drabenstadtj/musicplayer/ui/screens.py

import curses
import unicodedata
from ui.theme import *
from player.album_art import AlbumArtDisplay
from player.bluetooth import BluetoothManager

def display_width(text):
    """Calculate the display width of a string, accounting for wide characters"""
    width = 0
    for char in text:
        if unicodedata.east_asian_width(char) in ('F', 'W'):
            width += 2  # Full-width or Wide characters
        else:
            width += 1  # Normal width
    return width

def truncate_to_width(text, max_width):
    """Truncate text to fit within max_width, accounting for wide characters"""
    if display_width(text) <= max_width:
        return text

    current_width = 0
    result = ""
    ellipsis = "..."
    ellipsis_width = display_width(ellipsis)

    for char in text:
        char_width = 2 if unicodedata.east_asian_width(char) in ('F', 'W') else 1
        if current_width + char_width + ellipsis_width > max_width:
            return result + ellipsis
        result += char
        current_width += char_width

    return result

class BaseScreen:
    """Base class for all screens"""
    def __init__(self, stdscr):
        self.stdscr = stdscr
        self.height, self.width = stdscr.getmaxyx()
        self._pending_action = None

    def draw_status_bar(self, text, battery_percent=None):
        """Draw status bar at top"""
        self.stdscr.addstr(0, 0, " " * (self.width - 1))
        self.stdscr.addstr(0, 2, text, curses.color_pair(COLOR_STATUS) | curses.A_BOLD)

        if battery_percent is not None:
            battery_text = f"{battery_percent}% {SYMBOL_BATTERY}"
            self.stdscr.addstr(0, self.width - len(battery_text) - 2,
                             battery_text, curses.color_pair(COLOR_STATUS))

    def draw_footer(self, btn1="", btn2="", btn3="", btn4=""):
        """Draw footer with evenly spaced GPIO button labels

        Displays 4 button actions evenly spaced across the bottom
        to match the physical GPIO button layout (left to right).
        """
        footer_y = self.height - 1
        self.stdscr.addstr(footer_y, 0, " " * (self.width - 1))

        labels = [btn1, btn2, btn3, btn4]

        # Calculate positions to distribute evenly across the width
        # Place at 1/8, 3/8, 5/8, 7/8 of width (centered in each quarter)
        positions = [
            self.width // 8,
            (self.width * 3) // 8,
            (self.width * 5) // 8,
            (self.width * 7) // 8
        ]

        for i, label in enumerate(labels):
            if label:  # Only show if label is provided
                # Center the label at its position
                x_pos = positions[i] - len(label) // 2
                x_pos = max(0, min(x_pos, self.width - len(label) - 1))
                try:
                    self.stdscr.addstr(footer_y, x_pos, label)
                except:
                    pass  # Ignore if text doesn't fit

    def draw(self):
        """Override this in subclasses"""
        pass

    def handle_input(self, key):
        """Override this in subclasses. Return False to exit screen."""
        return True
    
    # Button methods - override in subclasses
    def on_up(self):
        """Handle UP button"""
        pass
    
    def on_down(self):
        """Handle DOWN button"""
        pass
    
    def on_select(self):
        """Handle SELECT button"""
        pass
    
    def on_back(self):
        """Handle BACK button"""
        pass


class MainMenuScreen(BaseScreen):
    """Main menu screen"""
    def __init__(self, stdscr):
        super().__init__(stdscr)
        self.menu_items = ["Albums", "Playlists", "Artists", "Settings"]
        self.selected = 0

    def draw(self):
        self.stdscr.clear()
        self.draw_status_bar(f"{SYMBOL_MUSIC} MUSIC PLAYER")

        # Draw menu items
        start_y = 3
        for i, item in enumerate(self.menu_items):
            y = start_y + (i * 2)
            if i == self.selected:
                self.stdscr.addstr(y, 8, f"> {item}",
                                 curses.color_pair(COLOR_SELECTED) | curses.A_BOLD)
            else:
                self.stdscr.addstr(y, 10, item, curses.color_pair(COLOR_NORMAL))

        self.draw_footer("↑", "↓", "Enter", "Quit")
        self.stdscr.refresh()

    def handle_input(self, key):
        if key == curses.KEY_UP:
            self.selected = max(0, self.selected - 1)
        elif key == curses.KEY_DOWN:
            self.selected = min(len(self.menu_items) - 1, self.selected + 1)
        elif key == ord('\n'):  # Enter key
            return self.menu_items[self.selected]  # Return selected menu
        elif key == ord('q') or key == ord('Q'):
            return False
        return True
    
    # Button support
    def on_up(self):
        self.selected = max(0, self.selected - 1)
        self.draw()
    
    def on_down(self):
        self.selected = min(len(self.menu_items) - 1, self.selected + 1)
        self.draw()
    
    def on_select(self):
        self._pending_action = self.menu_items[self.selected]
    
    def on_back(self):
        # On main menu, back does nothing (use long-press to quit)
        pass


class AlbumBrowserScreen(BaseScreen):
    """Album browser screen (full width)"""
    def __init__(self, stdscr, albums):
        super().__init__(stdscr)
        self.albums = albums
        self.album_index = 0
        self.scroll_offset = 0
        self.scroll_frame = 0
        self.last_album_index = 0

    def _get_scrolled_text(self, text, max_width, is_selected):
        """Get scrolling text for selected items with truncated content

        Args:
            text: Text to scroll
            max_width: Maximum display width
            is_selected: Whether this item is selected
        """
        text_width = display_width(text)

        if not is_selected or text_width <= max_width:
            # Not selected or fits within width - no scrolling needed
            return truncate_to_width(text, max_width)

        # Increment scroll offset
        self.scroll_offset = (self.scroll_offset + 1) % (text_width + 3)

        # Create circular scrolling effect
        # Add padding between end and start
        scrolling_text = text + "   " + text

        # Calculate starting position in the scrolling text
        start_offset = self.scroll_offset

        # Extract visible portion
        visible_text = ""
        current_width = 0
        char_index = 0

        # Skip to starting offset
        temp_offset = 0
        while temp_offset < start_offset and char_index < len(scrolling_text):
            char = scrolling_text[char_index]
            char_width = 2 if unicodedata.east_asian_width(char) in ('F', 'W') else 1
            temp_offset += char_width
            char_index += 1

        # Collect visible characters
        while current_width < max_width and char_index < len(scrolling_text):
            char = scrolling_text[char_index]
            char_width = 2 if unicodedata.east_asian_width(char) in ('F', 'W') else 1
            if current_width + char_width > max_width:
                break
            visible_text += char
            current_width += char_width
            char_index += 1

        return visible_text

    def draw(self):
        # Reset scroll if selection changed
        if self.album_index != self.last_album_index:
            self.scroll_offset = 0
            self.scroll_frame = 0
            self.last_album_index = self.album_index

        self.stdscr.clear()
        self.draw_status_bar("Albums")

        # Draw albums (full width)
        self.stdscr.addstr(2, 2, "Albums:", curses.A_BOLD)
        start = max(0, self.album_index - 5)
        for i in range(start, min(len(self.albums), start + 10)):
            y = 4 + (i - start)
            if y >= self.height - 2:
                break

            # Format album display with right-justified artist
            album = self.albums[i]
            artist = album.get('artist', 'Unknown Artist')
            album_name = album['name']

            # Calculate available space (full width)
            is_selected = i == self.album_index
            prefix = "> " if is_selected else "  "
            x_start = 2

            # Calculate max width for content (full width of screen)
            max_line_width = self.width - x_start - 2 - display_width(prefix)

            # Reserve space for artist (right-aligned) - use 40% of width
            artist_width = int(max_line_width * 0.4)
            album_width = max_line_width - artist_width - 1  # -1 for space separator

            # Truncate or scroll artist (right side)
            artist_display = truncate_to_width(artist, artist_width)
            artist_display_width = display_width(artist_display)

            # Display album and artist
            if is_selected:
                # For selected item, check if scrolling is needed
                full_text = f"{album_name} - {artist}"
                full_text_width = display_width(full_text)

                if full_text_width > max_line_width:
                    # Scroll the combined text
                    display_text = self._get_scrolled_text(full_text, max_line_width, True)
                else:
                    # Fits without scrolling - maintain right-justified layout
                    album_display = truncate_to_width(album_name, album_width)
                    album_display_width = display_width(album_display)

                    padding_needed = max_line_width - album_display_width - artist_display_width - 1
                    if padding_needed < 0:
                        padding_needed = 0

                    display_text = album_display + (" " * padding_needed) + " " + artist_display

                self.stdscr.addstr(y, x_start, f"{prefix}{display_text}",
                                 curses.color_pair(COLOR_SELECTED) | curses.A_BOLD)
            else:
                # Not selected - show album left-aligned, artist right-aligned
                album_display = truncate_to_width(album_name, album_width)
                album_display_width = display_width(album_display)

                # Calculate padding to right-justify artist
                padding_needed = max_line_width - album_display_width - artist_display_width - 1
                if padding_needed < 0:
                    padding_needed = 0

                display_text = album_display + (" " * padding_needed) + " " + artist_display

                self.stdscr.addstr(y, x_start, f"{prefix}{display_text}",
                                 curses.color_pair(COLOR_NORMAL))

        self.draw_footer("↑", "↓", "Select", "Back")
        self.stdscr.refresh()

    def handle_input(self, key):
        if key == curses.KEY_UP:
            self.album_index = max(0, self.album_index - 1)

        elif key == curses.KEY_DOWN:
            self.album_index = min(len(self.albums) - 1, self.album_index + 1)

        elif key == ord('\n'):  # Enter
            return ("select_album", self.albums[self.album_index])

        elif key == curses.KEY_BACKSPACE or key == 127:
            return "back"

        elif key == ord('q') or key == ord('Q'):
            return False

        return True

    # Button support
    def on_up(self):
        self.album_index = max(0, self.album_index - 1)
        self.draw()

    def on_down(self):
        self.album_index = min(len(self.albums) - 1, self.album_index + 1)
        self.draw()

    def on_select(self):
        self._pending_action = ("select_album", self.albums[self.album_index])

    def on_back(self):
        self._pending_action = "back"


class SongListScreen(BaseScreen):
    """Song list screen (full width)"""
    def __init__(self, stdscr, album, songs):
        super().__init__(stdscr)
        self.album = album
        self.songs = songs
        self.song_index = 0
        self.scroll_offset = 0
        self.scroll_frame = 0
        self.last_song_index = 0

    def _get_scrolled_text(self, text, max_width, is_selected):
        """Get scrolling text for selected items with truncated content"""
        text_width = display_width(text)

        if not is_selected or text_width <= max_width:
            return truncate_to_width(text, max_width)

        self.scroll_offset = (self.scroll_offset + 1) % (text_width + 3)
        scrolling_text = text + "   " + text
        start_offset = self.scroll_offset

        visible_text = ""
        current_width = 0
        char_index = 0

        temp_offset = 0
        while temp_offset < start_offset and char_index < len(scrolling_text):
            char = scrolling_text[char_index]
            char_width = 2 if unicodedata.east_asian_width(char) in ('F', 'W') else 1
            temp_offset += char_width
            char_index += 1

        while current_width < max_width and char_index < len(scrolling_text):
            char = scrolling_text[char_index]
            char_width = 2 if unicodedata.east_asian_width(char) in ('F', 'W') else 1
            if current_width + char_width > max_width:
                break
            visible_text += char
            current_width += char_width
            char_index += 1

        return visible_text

    def draw(self):
        # Reset scroll if selection changed
        if self.song_index != self.last_song_index:
            self.scroll_offset = 0
            self.scroll_frame = 0
            self.last_song_index = self.song_index

        self.stdscr.clear()
        album_name = self.album.get('name', 'Unknown Album')
        self.draw_status_bar(truncate_to_width(album_name, self.width - 10))

        # Draw songs (full width)
        self.stdscr.addstr(2, 2, "Songs:", curses.A_BOLD)
        start = max(0, self.song_index - 5)
        for i in range(start, min(len(self.songs), start + 10)):
            y = 4 + (i - start)
            if y >= self.height - 2:
                break

            song = self.songs[i]
            track_num = song.get('track', '')
            title = song.get('title', 'Unknown')
            artist = song.get('artist', 'Unknown Artist')

            # Build display text with track number if available
            if track_num:
                full_text = f"{track_num}. {title} - {artist}"
            else:
                full_text = f"{title} - {artist}"

            is_selected = i == self.song_index
            prefix = "> " if is_selected else "  "
            x_start = 2

            # Calculate max width for content (full width)
            max_line_width = self.width - x_start - 2 - display_width(prefix)

            # Scroll or truncate combined text
            if is_selected:
                display_text = self._get_scrolled_text(full_text, max_line_width, True)
            else:
                display_text = truncate_to_width(full_text, max_line_width)

            if is_selected:
                self.stdscr.addstr(y, x_start, f"{prefix}{display_text}",
                                 curses.color_pair(COLOR_SELECTED) | curses.A_BOLD)
            else:
                self.stdscr.addstr(y, x_start, f"{prefix}{display_text}",
                                 curses.color_pair(COLOR_NORMAL))

        self.draw_footer("↑", "↓", "Play", "Back")
        self.stdscr.refresh()

    def handle_input(self, key):
        if key == curses.KEY_UP:
            self.song_index = max(0, self.song_index - 1)

        elif key == curses.KEY_DOWN:
            self.song_index = min(len(self.songs) - 1, self.song_index + 1)

        elif key == ord('\n'):  # Enter
            return ("play_song", self.songs[self.song_index])

        elif key == curses.KEY_BACKSPACE or key == 127:
            return "back"

        elif key == ord('q') or key == ord('Q'):
            return False

        return True

    # Button support
    def on_up(self):
        self.song_index = max(0, self.song_index - 1)
        self.draw()

    def on_down(self):
        self.song_index = min(len(self.songs) - 1, self.song_index + 1)
        self.draw()

    def on_select(self):
        self._pending_action = ("play_song", self.songs[self.song_index])

    def on_back(self):
        self._pending_action = "back"


class NowPlayingScreen(BaseScreen):
    """Now playing screen"""
    def __init__(self, stdscr, audio_player, navidrome_client=None):
        super().__init__(stdscr)
        self.player = audio_player
        self.client = navidrome_client
        self.album_art = AlbumArtDisplay()
        self.current_art_path = None
        self.last_song_id = None  # Track which song we downloaded art for

    def draw(self):
        self.stdscr.clear()

        # Show volume in header
        vol_percent = int(self.player.volume)
        header_text = f"Now Playing - Vol: {vol_percent}%"
        self.draw_status_bar(header_text)

        if self.player.current_song:
            song = self.player.current_song

            title = song.get('title', 'Unknown')
            artist = song.get('artist', 'Unknown Artist')
            album = song.get('album', 'Unknown Album')

            # Download album art only once per song
            song_id = song.get('id')
            if self.client and song_id and song_id != self.last_song_id:
                # Try different fields that might contain cover art ID
                cover_art_id = song.get('coverArt') or song.get('albumId') or song_id
                if cover_art_id:
                    try:
                        cover_art_url = self.client.get_cover_art_url(cover_art_id, size=200)
                        if cover_art_url:
                            # Download and cache the album art
                            art_path = self.album_art.download_cover_art(cover_art_url, cover_art_id)
                            if art_path:
                                self.current_art_path = art_path
                    except Exception as e:
                        # Silently fail - album art is optional
                        pass
                    finally:
                        self.last_song_id = song_id

            # Display album art if available
            art_width = 20
            art_height = 10
            art_x_offset = 2
            info_x_offset = art_x_offset + art_width + 2

            # Try to display album art
            if self.current_art_path:
                try:
                    art_lines = self.album_art.get_ascii_art(self.current_art_path, art_width, art_height)
                    art_y = 3
                    for i, line in enumerate(art_lines):
                        if art_y + i < self.height - 2:
                            try:
                                self.stdscr.addstr(art_y + i, art_x_offset, line[:art_width])
                            except:
                                pass  # Ignore errors from characters that don't fit
                except:
                    pass  # Silently fail if album art can't be displayed

            # Song info
            info_y = 3
            max_text_width = self.width - info_x_offset - 2

            self.stdscr.addstr(info_y, info_x_offset, "Title:", curses.A_BOLD)
            self.stdscr.addstr(info_y + 1, info_x_offset, truncate_to_width(title, max_text_width),
                             curses.color_pair(COLOR_PLAYING))

            self.stdscr.addstr(info_y + 3, info_x_offset, "Artist:", curses.A_BOLD)
            self.stdscr.addstr(info_y + 4, info_x_offset, truncate_to_width(artist, max_text_width))

            self.stdscr.addstr(info_y + 6, info_x_offset, "Album:", curses.A_BOLD)
            self.stdscr.addstr(info_y + 7, info_x_offset, truncate_to_width(album, max_text_width))

            # Status
            status = f"{SYMBOL_PLAYING} PLAYING" if not self.player.is_paused else f"{SYMBOL_PAUSED} PAUSED"
            self.stdscr.addstr(info_y + 10, info_x_offset, status,
                             curses.color_pair(COLOR_PLAYING) | curses.A_BOLD)
        else:
            self.stdscr.addstr(self.height // 2, 2, "No song playing")

        self.draw_footer("Vol+", "Vol-", "Pause", "Exit")
        self.stdscr.refresh()

    def handle_input(self, key):
        if key == ord(' '):  # Spacebar
            self.player.toggle_pause()
        elif key == curses.KEY_UP:
            self.player.volume_up()
        elif key == curses.KEY_DOWN:
            self.player.volume_down()
        elif key == curses.KEY_BACKSPACE or key == 127:
            return "back"
        elif key == ord('q') or key == ord('Q'):
            return False
        return True

    # Button support
    def on_up(self):
        self.player.volume_up()
        self.draw()

    def on_down(self):
        self.player.volume_down()
        self.draw()
    
    def on_select(self):
        self.player.toggle_pause()
        self.draw()
    
    def on_back(self):
        self._pending_action = "back"

    def cleanup(self):
        """Clean up album art temporary files"""
        if self.album_art:
            self.album_art.cleanup()


class BluetoothSettingsScreen(BaseScreen):
    """Bluetooth audio settings screen"""
    def __init__(self, stdscr):
        super().__init__(stdscr)
        self.bt = BluetoothManager()
        self.devices = []
        self.selected = 0
        self.scanning = False
        self.status_message = ""
        self.connected_device = None
        self._refresh_devices()

    def _refresh_devices(self):
        """Refresh the device list"""
        if not self.bt.bluetoothctl_available:
            self.status_message = "Bluetooth not available"
            return

        # Get connected devices
        connected = self.bt.get_connected_devices()
        if connected:
            self.connected_device = connected[0]  # First connected device

        # Get all known devices
        self.devices = self.bt.scan_devices(duration=0)  # Quick list of known devices
        self.selected = min(self.selected, max(0, len(self.devices) - 1))

    def draw(self):
        self.stdscr.clear()
        self.draw_status_bar("Bluetooth Audio")

        if not self.bt.bluetoothctl_available:
            self.stdscr.addstr(3, 2, "Bluetooth not available on this system", curses.A_BOLD)
            self.draw_footer("", "", "", "Back")
            self.stdscr.refresh()
            return

        # Show connected device
        y = 3
        if self.connected_device:
            mac, name = self.connected_device
            self.stdscr.addstr(y, 2, "Connected:", curses.A_BOLD)
            self.stdscr.addstr(y, 14, f"{name}", curses.color_pair(COLOR_PLAYING))
            y += 1
            self.stdscr.addstr(y, 2, f"({mac})", curses.color_pair(COLOR_NORMAL) | curses.A_DIM)
            y += 2
        else:
            self.stdscr.addstr(y, 2, "Not connected to any device", curses.A_DIM)
            y += 2

        # Status message
        if self.status_message:
            self.stdscr.addstr(y, 2, self.status_message, curses.color_pair(COLOR_PLAYING))
            y += 1

        if self.scanning:
            self.stdscr.addstr(y, 2, "Scanning for devices...", curses.A_BOLD)
            y += 2

        # Device list
        self.stdscr.addstr(y, 2, "Options:", curses.A_BOLD)
        y += 2

        # Always show "Scan for devices" as first option
        scan_selected = self.selected == 0
        scan_text = "> [Scan for devices]" if scan_selected else "  [Scan for devices]"
        if scan_selected:
            self.stdscr.addstr(y, 4, scan_text, curses.color_pair(COLOR_SELECTED) | curses.A_BOLD)
        else:
            self.stdscr.addstr(y, 4, scan_text, curses.color_pair(COLOR_NORMAL))
        y += 1

        # Show connected device disconnect option if connected
        if self.connected_device:
            disconnect_selected = self.selected == 1
            mac, name = self.connected_device
            disconnect_text = f"> [Disconnect {name}]" if disconnect_selected else f"  [Disconnect {name}]"
            if disconnect_selected:
                self.stdscr.addstr(y, 4, truncate_to_width(disconnect_text, self.width - 6),
                                 curses.color_pair(COLOR_SELECTED) | curses.A_BOLD)
            else:
                self.stdscr.addstr(y, 4, truncate_to_width(disconnect_text, self.width - 6),
                                 curses.color_pair(COLOR_NORMAL))
            y += 1

        y += 1
        if self.devices:
            self.stdscr.addstr(y, 2, "Devices:", curses.A_BOLD)
            y += 1

        # Calculate offset for device list items
        device_offset = 2 if self.connected_device else 1

        if self.devices:
            for i, (mac, name, paired) in enumerate(self.devices):
                # Make sure we don't draw beyond the footer
                if y >= self.height - 2:
                    break

                list_index = i + device_offset
                is_selected = list_index == self.selected
                prefix = "> " if is_selected else "  "

                # Show device name
                status = ""
                if self.bt.is_connected(mac):
                    status = " [CONNECTED]"
                    color = COLOR_PLAYING
                elif paired:
                    status = " [PAIRED]"
                    color = COLOR_SELECTED
                else:
                    color = COLOR_NORMAL

                display_text = f"{prefix}{name}{status}"
                max_width = self.width - 6

                if is_selected:
                    self.stdscr.addstr(y, 4, truncate_to_width(display_text, max_width),
                                     curses.color_pair(COLOR_SELECTED) | curses.A_BOLD)
                else:
                    self.stdscr.addstr(y, 4, truncate_to_width(display_text, max_width),
                                     curses.color_pair(color))

                y += 1

        self.draw_footer("↑", "↓", "Select", "Back")
        self.stdscr.refresh()

    def handle_input(self, key):
        # Calculate max selection index
        device_offset = 2 if self.connected_device else 1
        max_selection = len(self.devices) + device_offset - 1

        if key == curses.KEY_UP:
            self.selected = max(0, self.selected - 1)

        elif key == curses.KEY_DOWN:
            self.selected = min(max_selection, self.selected + 1)

        elif key == ord('\n'):  # Enter/SELECT button
            if self.selected == 0:
                # Scan for devices option
                self.scanning = True
                self.status_message = "Scanning..."
                self.draw()
                self.stdscr.refresh()

                self.devices = self.bt.scan_devices(duration=5)
                self.scanning = False
                self.status_message = f"Found {len(self.devices)} device(s)"
                self._refresh_devices()

            elif self.connected_device and self.selected == 1:
                # Disconnect option
                mac, name = self.connected_device
                self.status_message = f"Disconnecting from {name}..."
                self.draw()
                self.stdscr.refresh()

                if self.bt.disconnect_device(mac):
                    self.status_message = "Disconnected"
                    self.connected_device = None
                else:
                    self.status_message = "Failed to disconnect"
                self._refresh_devices()

            else:
                # Connect to a device
                device_index = self.selected - device_offset
                if 0 <= device_index < len(self.devices):
                    mac, name, paired = self.devices[device_index]

                    self.status_message = f"Connecting to {name}..."
                    self.draw()
                    self.stdscr.refresh()

                    # Pair if not paired
                    if not paired:
                        self.status_message = "Pairing..."
                        self.draw()
                        self.stdscr.refresh()

                        if not self.bt.pair_device(mac):
                            self.status_message = "Pairing failed"
                            return True

                    # Connect
                    if self.bt.connect_device(mac):
                        self.status_message = f"Connected to {name}"
                        self.connected_device = (mac, name)

                        # Set as default audio sink
                        self.bt.set_as_default_sink()
                    else:
                        self.status_message = "Connection failed"

                    self._refresh_devices()

        elif key == curses.KEY_BACKSPACE or key == 127:
            return "back"

        elif key == ord('q') or key == ord('Q'):
            return False

        return True

    # Button support
    def on_up(self):
        # UP button: Navigate up
        self.handle_input(curses.KEY_UP)
        self.draw()

    def on_down(self):
        # DOWN button: Navigate down
        self.handle_input(curses.KEY_DOWN)
        self.draw()

    def on_select(self):
        # SELECT button: Choose selected option (scan/disconnect/connect)
        self.handle_input(ord('\n'))
        self.draw()

    def on_back(self):
        self._pending_action = "back"


class ArtistBrowserScreen(BaseScreen):
    """Artist browser screen - displays list of artists with letter categories"""
    def __init__(self, stdscr, artists):
        super().__init__(stdscr)
        self.artists = sorted(artists, key=lambda x: x.get('name', '').lower())
        self.artist_index = 0
        self.scroll_offset = 0
        self.scroll_frame = 0
        self.last_artist_index = 0

        # Letter selector mode
        self.letter_selector_mode = False
        self.selected_letter_index = 0

        # Build letter category index
        self.letter_categories = {}
        self.category_list = []

        for i, artist in enumerate(self.artists):
            name = artist.get('name', '')
            if name:
                first_letter = name[0].upper()
                # Group non-alphabetic characters as '#'
                if not first_letter.isalpha():
                    first_letter = '#'

                if first_letter not in self.letter_categories:
                    self.letter_categories[first_letter] = i
                    self.category_list.append(first_letter)

        # Sort categories (# first, then A-Z)
        self.category_list.sort(key=lambda x: ('0' if x == '#' else x))
        self.current_category_index = 0

    def _get_scrolled_text(self, text, max_width, is_selected):
        """Get scrolling text for selected items"""
        text_width = display_width(text)

        if not is_selected or text_width <= max_width:
            return truncate_to_width(text, max_width)

        # Create circular scrolling effect
        scrolling_text = text + "   " + text  # Add spacing before loop

        self.scroll_frame += 1
        if self.scroll_frame >= 8:  # Scroll every 8 frames (~0.8s)
            self.scroll_offset = (self.scroll_offset + 1) % (text_width + 3)
            self.scroll_frame = 0

        # Calculate which part of scrolling_text to show
        start_offset = self.scroll_offset
        visible_text = ""
        current_width = 0
        char_index = 0

        # Skip to starting offset
        temp_offset = 0
        while temp_offset < start_offset and char_index < len(scrolling_text):
            char = scrolling_text[char_index]
            char_width = 2 if unicodedata.east_asian_width(char) in ('F', 'W') else 1
            temp_offset += char_width
            char_index += 1

        # Collect visible characters
        while current_width < max_width and char_index < len(scrolling_text):
            char = scrolling_text[char_index]
            char_width = 2 if unicodedata.east_asian_width(char) in ('F', 'W') else 1
            if current_width + char_width > max_width:
                break
            visible_text += char
            current_width += char_width
            char_index += 1

        return visible_text

    def get_current_letter(self):
        """Get the letter category for the current artist"""
        if not self.artists or self.artist_index >= len(self.artists):
            return ''
        name = self.artists[self.artist_index].get('name', '')
        if name:
            first_letter = name[0].upper()
            return '#' if not first_letter.isalpha() else first_letter
        return ''

    def jump_to_next_category(self):
        """Jump to the next letter category (forward: A->B->C)"""
        if not self.category_list:
            return

        # Find current category
        current_letter = self.get_current_letter()
        try:
            current_idx = self.category_list.index(current_letter)
            # Jump to next category (wrap around)
            next_idx = (current_idx + 1) % len(self.category_list)
            next_letter = self.category_list[next_idx]
            # Set artist_index to first artist in that category
            self.artist_index = self.letter_categories[next_letter]
        except (ValueError, KeyError):
            # If current letter not in list, jump to first category
            if self.category_list:
                self.artist_index = self.letter_categories[self.category_list[0]]

    def jump_to_prev_category(self):
        """Jump to the previous letter category (backward: C->B->A)"""
        if not self.category_list:
            return

        # Find current category
        current_letter = self.get_current_letter()
        try:
            current_idx = self.category_list.index(current_letter)
            # Jump to previous category (wrap around)
            prev_idx = (current_idx - 1) % len(self.category_list)
            prev_letter = self.category_list[prev_idx]
            # Set artist_index to first artist in that category
            self.artist_index = self.letter_categories[prev_letter]
        except (ValueError, KeyError):
            # If current letter not in list, jump to last category
            if self.category_list:
                self.artist_index = self.letter_categories[self.category_list[-1]]

    def toggle_letter_selector_mode(self):
        """Toggle between artist browsing and letter selection mode"""
        self.letter_selector_mode = not self.letter_selector_mode
        if self.letter_selector_mode:
            # Set selected letter to current category
            current_letter = self.get_current_letter()
            try:
                self.selected_letter_index = self.category_list.index(current_letter)
            except ValueError:
                self.selected_letter_index = 0

    def navigate_letter_selector(self, direction):
        """Navigate through letters in selector mode"""
        if not self.category_list:
            return

        if direction == "left":
            self.selected_letter_index = (self.selected_letter_index - 1) % len(self.category_list)
        elif direction == "right":
            self.selected_letter_index = (self.selected_letter_index + 1) % len(self.category_list)

    def jump_to_selected_letter(self):
        """Jump to the currently selected letter and exit selector mode"""
        if self.category_list and 0 <= self.selected_letter_index < len(self.category_list):
            selected_letter = self.category_list[self.selected_letter_index]
            self.artist_index = self.letter_categories[selected_letter]
            self.letter_selector_mode = False

    def draw(self):
        # Reset scroll if selection changed
        if self.artist_index != self.last_artist_index:
            self.scroll_offset = 0
            self.scroll_frame = 0
            self.last_artist_index = self.artist_index

        self.stdscr.clear()

        # Show current letter category in status bar
        if self.letter_selector_mode:
            status_text = "Letter Select Mode"
        else:
            current_letter = self.get_current_letter()
            status_text = f"Artists [{current_letter}]" if current_letter else "Artists"
        self.draw_status_bar(status_text)

        # Draw artists (full width)
        self.stdscr.addstr(2, 2, "Artists:", curses.A_BOLD)

        # Show letter category indicators on line 3
        if self.category_list:
            x_pos = 2
            for idx, letter in enumerate(self.category_list):
                # Highlight selected letter in selector mode
                if self.letter_selector_mode and idx == self.selected_letter_index:
                    self.stdscr.addstr(3, x_pos, letter, curses.color_pair(COLOR_SELECTED) | curses.A_BOLD)
                else:
                    self.stdscr.addstr(3, x_pos, letter, curses.color_pair(COLOR_NORMAL))
                x_pos += len(letter) + 1  # letter + space

                # Stop if we run out of space
                if x_pos >= self.width - 4:
                    break

        start = max(0, self.artist_index - 4)
        y = 5  # Starting y position for artist list

        for i in range(start, min(len(self.artists), start + 9)):
            if y >= self.height - 2:
                break

            artist = self.artists[i]
            artist_name = artist.get('name', 'Unknown Artist')
            album_count = artist.get('albumCount', 0)

            # Check if we need to show a category header
            show_header = False
            if i == 0:
                # First artist ever
                show_header = True
            elif i > 0:
                # Check if letter changed from previous artist
                prev_name = self.artists[i-1].get('name', ' ')
                curr_letter = artist_name[0].upper() if artist_name and artist_name[0].isalpha() else '#'
                prev_letter = prev_name[0].upper() if prev_name and prev_name[0].isalpha() else '#'
                if curr_letter != prev_letter:
                    show_header = True

            if show_header:
                letter = artist_name[0].upper() if artist_name and artist_name[0].isalpha() else '#'
                # Draw category header
                self.stdscr.addstr(y, 2, f"--- {letter} ---", curses.A_DIM)
                y += 1
                if y >= self.height - 2:
                    break

            # Format display
            is_selected = i == self.artist_index
            prefix = "> " if is_selected else "  "
            x_start = 2

            # Calculate max width for content
            max_line_width = self.width - x_start - 2 - display_width(prefix)

            # Add album count
            count_text = f" ({album_count} albums)"
            display_text = artist_name + count_text

            if is_selected:
                scrolled_text = self._get_scrolled_text(display_text, max_line_width, True)
                self.stdscr.addstr(y, x_start, f"{prefix}{scrolled_text}",
                                 curses.color_pair(COLOR_SELECTED) | curses.A_BOLD)
            else:
                truncated_text = truncate_to_width(display_text, max_line_width)
                self.stdscr.addstr(y, x_start, f"{prefix}{truncated_text}",
                                 curses.color_pair(COLOR_NORMAL))

            y += 1  # Move to next line for next artist

        # Show different footer based on mode
        if self.letter_selector_mode:
            self.draw_footer("←Letter", "Letter→", "Jump", "Cancel")
        else:
            self.draw_footer("↑", "↓", "Select", "Back")
        self.stdscr.refresh()

    def handle_input(self, key):
        # In letter selector mode, use different key bindings
        if self.letter_selector_mode:
            if key == curses.KEY_LEFT:
                self.navigate_letter_selector("left")
            elif key == curses.KEY_RIGHT:
                self.navigate_letter_selector("right")
            elif key == ord('\n'):  # Enter - jump to selected letter
                self.jump_to_selected_letter()
            elif key == curses.KEY_BACKSPACE or key == 127:  # Back - exit selector mode
                self.letter_selector_mode = False
            elif key == ord('q') or key == ord('Q'):
                return False
        else:
            # Normal artist browsing mode
            if key == curses.KEY_UP:
                self.artist_index = max(0, self.artist_index - 1)

            elif key == curses.KEY_DOWN:
                self.artist_index = min(len(self.artists) - 1, self.artist_index + 1)

            elif key == curses.KEY_LEFT or key == curses.KEY_RIGHT:
                # LEFT/RIGHT toggle letter selector mode
                self.toggle_letter_selector_mode()

            elif key == ord('\n'):  # Enter
                return ("select_artist", self.artists[self.artist_index])

            elif key == curses.KEY_BACKSPACE or key == 127:
                return "back"

            elif key == ord('q') or key == ord('Q'):
                return False

        return True

    # Button support
    def on_up(self):
        if self.letter_selector_mode:
            # In letter selector mode, UP navigates left through letters
            self.navigate_letter_selector("left")
        else:
            # Normal mode - navigate up in artist list
            self.artist_index = max(0, self.artist_index - 1)
        self.draw()

    def on_down(self):
        if self.letter_selector_mode:
            # In letter selector mode, DOWN navigates right through letters
            self.navigate_letter_selector("right")
        else:
            # Normal mode - navigate down in artist list
            self.artist_index = min(len(self.artists) - 1, self.artist_index + 1)
        self.draw()

    def on_select(self):
        if self.letter_selector_mode:
            # Confirm letter selection and exit mode
            self.jump_to_selected_letter()
            self.draw()
        else:
            # Normal select - choose artist
            self._pending_action = ("select_artist", self.artists[self.artist_index])

    def on_back(self):
        if self.letter_selector_mode:
            # Exit letter selector mode
            self.letter_selector_mode = False
            self.draw()
        else:
            # Normal back
            self._pending_action = "back"


class PlaylistBrowserScreen(BaseScreen):
    """Playlist browser screen - displays list of playlists"""
    def __init__(self, stdscr, playlists):
        super().__init__(stdscr)
        self.playlists = sorted(playlists, key=lambda x: x.get('name', '').lower())
        self.playlist_index = 0
        self.scroll_offset = 0
        self.scroll_frame = 0
        self.last_playlist_index = 0

    def _get_scrolled_text(self, text, max_width, is_selected):
        """Get scrolling text for selected items"""
        text_width = display_width(text)

        if not is_selected or text_width <= max_width:
            return truncate_to_width(text, max_width)

        # Create circular scrolling effect
        scrolling_text = text + "   " + text  # Add spacing before loop

        self.scroll_frame += 1
        if self.scroll_frame >= 8:  # Scroll every 8 frames (~0.8s)
            self.scroll_offset = (self.scroll_offset + 1) % (text_width + 3)
            self.scroll_frame = 0

        # Calculate which part of scrolling_text to show
        start_offset = self.scroll_offset
        visible_text = ""
        current_width = 0
        char_index = 0

        # Skip to starting offset
        temp_offset = 0
        while temp_offset < start_offset and char_index < len(scrolling_text):
            char = scrolling_text[char_index]
            char_width = 2 if unicodedata.east_asian_width(char) in ('F', 'W') else 1
            temp_offset += char_width
            char_index += 1

        # Collect visible characters
        while current_width < max_width and char_index < len(scrolling_text):
            char = scrolling_text[char_index]
            char_width = 2 if unicodedata.east_asian_width(char) in ('F', 'W') else 1
            if current_width + char_width > max_width:
                break
            visible_text += char
            current_width += char_width
            char_index += 1

        return visible_text

    def draw(self):
        # Reset scroll if selection changed
        if self.playlist_index != self.last_playlist_index:
            self.scroll_offset = 0
            self.scroll_frame = 0
            self.last_playlist_index = self.playlist_index

        self.stdscr.clear()
        self.draw_status_bar("Playlists")

        # Draw playlists (full width)
        self.stdscr.addstr(2, 2, "Playlists:", curses.A_BOLD)
        start = max(0, self.playlist_index - 5)
        for i in range(start, min(len(self.playlists), start + 10)):
            y = 4 + (i - start)
            if y >= self.height - 2:
                break

            playlist = self.playlists[i]
            playlist_name = playlist.get('name', 'Unknown Playlist')
            song_count = playlist.get('songCount', 0)

            # Format display
            is_selected = i == self.playlist_index
            prefix = "> " if is_selected else "  "
            x_start = 2

            # Calculate max width for content
            max_line_width = self.width - x_start - 2 - display_width(prefix)

            # Add song count
            count_text = f" ({song_count} songs)"
            display_text = playlist_name + count_text

            if is_selected:
                scrolled_text = self._get_scrolled_text(display_text, max_line_width, True)
                self.stdscr.addstr(y, x_start, f"{prefix}{scrolled_text}",
                                 curses.color_pair(COLOR_SELECTED) | curses.A_BOLD)
            else:
                truncated_text = truncate_to_width(display_text, max_line_width)
                self.stdscr.addstr(y, x_start, f"{prefix}{truncated_text}",
                                 curses.color_pair(COLOR_NORMAL))

        self.draw_footer("↑", "↓", "Select", "Back")
        self.stdscr.refresh()

    def handle_input(self, key):
        if key == curses.KEY_UP:
            self.playlist_index = max(0, self.playlist_index - 1)

        elif key == curses.KEY_DOWN:
            self.playlist_index = min(len(self.playlists) - 1, self.playlist_index + 1)

        elif key == ord('\n'):  # Enter
            return ("select_playlist", self.playlists[self.playlist_index])

        elif key == curses.KEY_BACKSPACE or key == 127:
            return "back"

        elif key == ord('q') or key == ord('Q'):
            return False

        return True

    # Button support
    def on_up(self):
        self.playlist_index = max(0, self.playlist_index - 1)
        self.draw()

    def on_down(self):
        self.playlist_index = min(len(self.playlists) - 1, self.playlist_index + 1)
        self.draw()

    def on_select(self):
        self._pending_action = ("select_playlist", self.playlists[self.playlist_index])

    def on_back(self):
        self._pending_action = "back"
